MR-DOS/TDR-avalanche/outputs/opengl.png

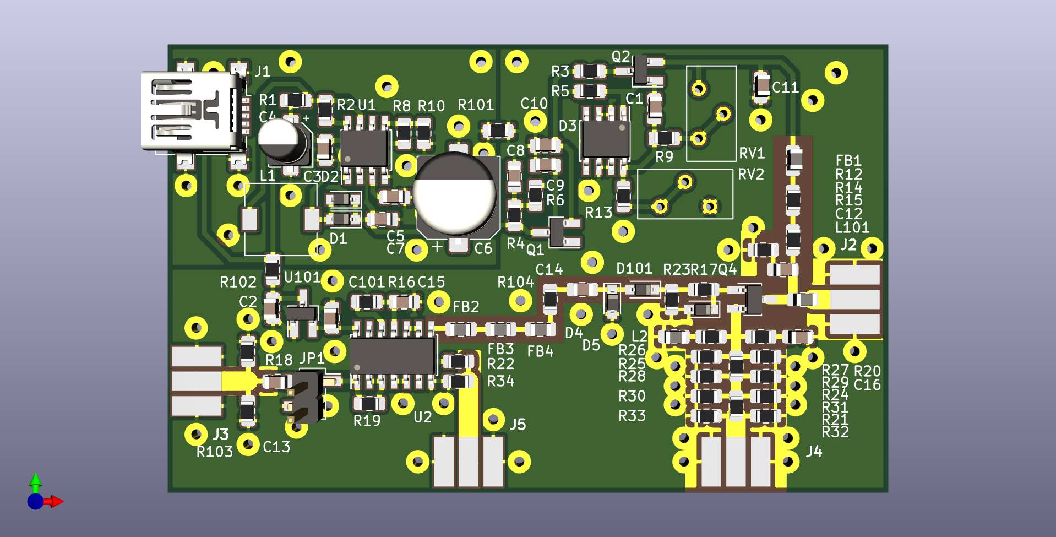
outputs/opengl.png
